guolic1/AirDAP/firmware/components/ota_manager/ota_manager.c

#include <stdbool.h>
#include <stddef.h>
#include <stdint.h>
#include <string.h>

#include "airdap_dap_ownership.h"
#include "airdap_device_identity.h"
#include "airdap_mode_state.h"
#include "airdap_ota.h"
#include "airdap_target_uart.h"
#include "freertos/FreeRTOS.h"
#include "freertos/semphr.h"
#include "esp_err.h"
#include "esp_ota_ops.h"
#include "esp_partition.h"
#include "esp_system.h"

typedef enum {
    OTA_SESSION_IDLE,
    OTA_SESSION_RECEIVING,
    OTA_SESSION_COMMITTED,
} ota_session_state_t;

typedef struct {
    const esp_partition_t *partition;
    esp_ota_handle_t handle;
    uint32_t expected_size;
    uint32_t written_size;
    ota_session_state_t state;
    void *connection;
    uint32_t owner_session;
    bool disconnected;
} ota_session_t;

static ota_session_t session;
static SemaphoreHandle_t session_mutex;

static bool lock_session(void)
{
    return session_mutex != NULL && xSemaphoreTake(session_mutex, portMAX_DELAY) == pdTRUE;
}

static void unlock_session(void)
{
    (void) xSemaphoreGive(session_mutex);
}

static bool authorized(const airdap_ota_client_t *client)
{
    return client == NULL || (client->connection != NULL && client->session_id != 0U &&
        client->authorize != NULL && client->authorize(client->connection, client->session_id));
}

static bool owns_session(const airdap_ota_client_t *client)
{
    return session.connection == (client == NULL ? NULL : client->connection) &&
        session.owner_session == (client == NULL ? 0U : client->session_id);
}

static void reset_session(void)
{
    memset(&session, 0, sizeof(session));
    session.state = OTA_SESSION_IDLE;
}

static bool restore_idle_mode(airdap_mode_event_t event)
{
    const airdap_mode_state_result_t mode_result =
        airdap_mode_state_transition(event);
    if (mode_result != AIRDAP_MODE_STATE_OK) {
        return false;
    }
    const airdap_dap_ownership_result_t ownership_result =
        airdap_dap_ownership_resume();
    return ownership_result == AIRDAP_DAP_OWNERSHIP_OK &&
        airdap_target_uart_resume() == ESP_OK;
}

static esp_err_t initialize_locked(void)
{
    esp_err_t abort_error = ESP_OK;
    if (session.state == OTA_SESSION_RECEIVING) {
        abort_error = esp_ota_abort(session.handle);
    }
    reset_session();
    if (airdap_mode_state_transition(AIRDAP_MODE_EVENT_OTA_RESET) !=
        AIRDAP_MODE_STATE_OK) {
        return ESP_ERR_INVALID_STATE;
    }
    const airdap_dap_ownership_result_t ownership_result =
        airdap_dap_ownership_resume();
    if (ownership_result != AIRDAP_DAP_OWNERSHIP_OK &&
        ownership_result != AIRDAP_DAP_OWNERSHIP_INVALID_STATE) {
        return ESP_ERR_INVALID_STATE;
    }
    return airdap_target_uart_resume() == ESP_OK ? abort_error : ESP_FAIL;
}

static bool debug_allowed_locked(void)
{
    airdap_mode_snapshot_t mode;
    return session.state == OTA_SESSION_IDLE &&
        airdap_mode_state_get(&mode) == AIRDAP_MODE_STATE_OK &&
        mode.ota == AIRDAP_OTA_IDLE;
}

static airdap_ota_status_t get_info_locked(airdap_ota_info_t *info)
{
    if (info == NULL) {
        return AIRDAP_OTA_STATUS_INVALID_ARGUMENT;
    }

    const esp_partition_t *partition = esp_ota_get_next_update_partition(NULL);
    const airdap_device_identity_t *identity = airdap_device_identity_get();
    if (partition == NULL || identity == NULL || partition->size > UINT32_MAX) {
        return AIRDAP_OTA_STATUS_INTERNAL_ERROR;
    }

    memset(info, 0, sizeof(*info));
    const esp_partition_t *running = esp_ota_get_running_partition();
    esp_ota_img_states_t running_state;
    if (running == NULL || esp_ota_get_state_partition(running, &running_state) != ESP_OK) {
        return AIRDAP_OTA_STATUS_INTERNAL_ERROR;
    }
    info->running_address = running->address;
    info->update_address = partition->address;
    info->running_valid = running_state == ESP_OTA_IMG_VALID;
    info->protocol_version = AIRDAP_OTA_PROTOCOL_VERSION;
    info->flags = AIRDAP_OTA_FLAG_ROLLBACK;
    info->max_image_size = (uint32_t) partition->size;
    size_t version_length = 0U;
    while (version_length < AIRDAP_OTA_VERSION_CAPACITY &&
           identity->firmware_version[version_length] != '\0') {
        ++version_length;
    }
    memcpy(info->running_version, identity->firmware_version, version_length);
    info->running_version[version_length] = '\0';
    return AIRDAP_OTA_STATUS_OK;
}

static airdap_ota_status_t begin_locked(const airdap_ota_client_t *client, uint32_t image_size)
{
    if (session.state != OTA_SESSION_IDLE) {
        return AIRDAP_OTA_STATUS_INVALID_STATE;
    }

    const esp_partition_t *partition = esp_ota_get_next_update_partition(NULL);
    if (partition == NULL || partition->size > UINT32_MAX) {
        return AIRDAP_OTA_STATUS_INTERNAL_ERROR;
    }
    if (image_size == 0U || image_size > partition->size) {
        return AIRDAP_OTA_STATUS_INVALID_SIZE;
    }

    if (airdap_mode_state_transition(AIRDAP_MODE_EVENT_OTA_STARTED) !=
        AIRDAP_MODE_STATE_OK) {
        return AIRDAP_OTA_STATUS_INTERNAL_ERROR;
    }

    const airdap_dap_ownership_result_t ownership_result =
        airdap_dap_ownership_suspend();
    if (ownership_result == AIRDAP_DAP_OWNERSHIP_BUSY) {
        return airdap_mode_state_transition(AIRDAP_MODE_EVENT_OTA_FAILED) ==
            AIRDAP_MODE_STATE_OK
            ? AIRDAP_OTA_STATUS_INVALID_STATE
            : AIRDAP_OTA_STATUS_INTERNAL_ERROR;
    }
    if (ownership_result != AIRDAP_DAP_OWNERSHIP_OK) {
        if (airdap_mode_state_transition(AIRDAP_MODE_EVENT_OTA_FAILED) !=
            AIRDAP_MODE_STATE_OK) {
            return AIRDAP_OTA_STATUS_INTERNAL_ERROR;
        }
        return AIRDAP_OTA_STATUS_INTERNAL_ERROR;
    }

    if (airdap_target_uart_suspend() != ESP_OK) {
        (void) restore_idle_mode(AIRDAP_MODE_EVENT_OTA_FAILED);
        return AIRDAP_OTA_STATUS_BUSY;
    }
    if (!authorized(client)) {
        (void) restore_idle_mode(AIRDAP_MODE_EVENT_OTA_FAILED);
        return AIRDAP_OTA_STATUS_UNAUTHENTICATED;
    }

    esp_ota_handle_t handle = 0U;
    if (esp_ota_begin(
            partition,
            OTA_WITH_SEQUENTIAL_WRITES,
            &handle) != ESP_OK) {
        if (handle != 0U) {
            (void) esp_ota_abort(handle);
        }
        (void) restore_idle_mode(AIRDAP_MODE_EVENT_OTA_FAILED);
        return AIRDAP_OTA_STATUS_INTERNAL_ERROR;
    }

    session.partition = partition;
    session.handle = handle;
    session.expected_size = image_size;
    session.written_size = 0U;
    session.state = OTA_SESSION_RECEIVING;
    session.connection = client == NULL ? NULL : client->connection;
    session.owner_session = client == NULL ? 0U : client->session_id;
    return AIRDAP_OTA_STATUS_OK;
}

static airdap_ota_status_t write_locked(
    uint32_t offset,
    const void *data,
    size_t size,
    uint32_t *next_offset)
{
    if (session.state != OTA_SESSION_RECEIVING) {
        return AIRDAP_OTA_STATUS_INVALID_STATE;
    }
    if (data == NULL || next_offset == NULL) {
        return AIRDAP_OTA_STATUS_INVALID_ARGUMENT;
    }
    if (offset != session.written_size) {
        return AIRDAP_OTA_STATUS_INVALID_OFFSET;
    }
    if (size == 0U || size > session.expected_size - session.written_size) {
        return AIRDAP_OTA_STATUS_INVALID_SIZE;
    }

    if (esp_ota_write(session.handle, data, size) != ESP_OK) {
        if (esp_ota_abort(session.handle) != ESP_OK) {
            return AIRDAP_OTA_STATUS_INTERNAL_ERROR;
        }
        reset_session();
        return restore_idle_mode(AIRDAP_MODE_EVENT_OTA_FAILED)
            ? AIRDAP_OTA_STATUS_WRITE_FAILED
            : AIRDAP_OTA_STATUS_INTERNAL_ERROR;
    }

    session.written_size += (uint32_t) size;
    *next_offset = session.written_size;
    return AIRDAP_OTA_STATUS_OK;
}

static airdap_ota_status_t commit_locked(const airdap_ota_client_t *client)
{
    if (session.state != OTA_SESSION_RECEIVING) {
        return AIRDAP_OTA_STATUS_INVALID_STATE;
    }
    if (session.written_size != session.expected_size) {
        return AIRDAP_OTA_STATUS_INCOMPLETE_IMAGE;
    }

    const esp_partition_t *partition = session.partition;
    const esp_ota_handle_t handle = session.handle;
    if (esp_ota_end(handle) != ESP_OK) {
        reset_session();
        return restore_idle_mode(AIRDAP_MODE_EVENT_OTA_FAILED)
            ? AIRDAP_OTA_STATUS_VALIDATION_FAILED
            : AIRDAP_OTA_STATUS_INTERNAL_ERROR;
    }
    if (!authorized(client)) {
        reset_session();
        (void) restore_idle_mode(AIRDAP_MODE_EVENT_OTA_FAILED);
        return AIRDAP_OTA_STATUS_UNAUTHENTICATED;
    }
    if (esp_ota_set_boot_partition(partition) != ESP_OK) {
        reset_session();
        return restore_idle_mode(AIRDAP_MODE_EVENT_OTA_FAILED)
            ? AIRDAP_OTA_STATUS_ACTIVATION_FAILED
            : AIRDAP_OTA_STATUS_INTERNAL_ERROR;
    }

    session.partition = partition;
    session.handle = 0U;
    session.expected_size = 0U;
    session.written_size = 0U;
    session.state = OTA_SESSION_COMMITTED;
    if (airdap_mode_state_transition(AIRDAP_MODE_EVENT_OTA_COMMITTED) !=
        AIRDAP_MODE_STATE_OK) {
        return AIRDAP_OTA_STATUS_INTERNAL_ERROR;
    }
    return AIRDAP_OTA_STATUS_OK;
}

static airdap_ota_status_t abort_locked(void)
{
    if (session.state == OTA_SESSION_IDLE) {
        return AIRDAP_OTA_STATUS_OK;
    }
    if (session.state == OTA_SESSION_COMMITTED) {
        return AIRDAP_OTA_STATUS_INVALID_STATE;
    }

    const esp_err_t error = esp_ota_abort(session.handle);
    if (error != ESP_OK) {
        return AIRDAP_OTA_STATUS_INTERNAL_ERROR;
    }
    reset_session();
    return restore_idle_mode(AIRDAP_MODE_EVENT_OTA_ABORTED)
        ? AIRDAP_OTA_STATUS_OK
        : AIRDAP_OTA_STATUS_INTERNAL_ERROR;
}

static airdap_ota_status_t reboot_locked(void)
{
    if (session.state != OTA_SESSION_COMMITTED) {
        return AIRDAP_OTA_STATUS_INVALID_STATE;
    }
    esp_restart();
    return AIRDAP_OTA_STATUS_OK;
}

esp_err_t airdap_ota_confirm_running_image(void)
{
    const esp_partition_t *running = esp_ota_get_running_partition();
    if (running == NULL) {
        return ESP_FAIL;
    }

    esp_ota_img_states_t state;
    const esp_err_t error = esp_ota_get_state_partition(running, &state);
    if (error != ESP_OK) {
        return error;
    }
    if (state == ESP_OTA_IMG_PENDING_VERIFY) {
        return esp_ota_mark_app_valid_cancel_rollback();
    }
    return ESP_OK;
}

esp_err_t airdap_ota_initialize(void)
{
    /* Called once by app_main before transports start. */
    if (session_mutex == NULL) session_mutex = xSemaphoreCreateMutex();
    if (!lock_session()) return ESP_FAIL;
    const esp_err_t result = initialize_locked();
    unlock_session();
    return result;
}

bool airdap_ota_debug_allowed(void)
{
    if (!lock_session()) return false;
    const bool result = debug_allowed_locked();
    unlock_session();
    return result;
}

airdap_ota_status_t airdap_ota_get_info(airdap_ota_info_t *info)
{
    if (!lock_session()) return AIRDAP_OTA_STATUS_INTERNAL_ERROR;
    const airdap_ota_status_t result = get_info_locked(info);
    unlock_session();
    return result;
}

airdap_ota_status_t airdap_ota_begin_for_client(
    const airdap_ota_client_t *client, uint32_t image_size)
{
    if (!lock_session()) return AIRDAP_OTA_STATUS_INTERNAL_ERROR;
    airdap_ota_status_t result;
    if (!authorized(client)) result = AIRDAP_OTA_STATUS_UNAUTHENTICATED;
    else if (session.state != OTA_SESSION_IDLE && !owns_session(client)) result = AIRDAP_OTA_STATUS_BUSY;
    else result = begin_locked(client, image_size);
    unlock_session();
    return result;
}

airdap_ota_status_t airdap_ota_begin(uint32_t image_size)
{
    return airdap_ota_begin_for_client(NULL, image_size);
}

airdap_ota_status_t airdap_ota_write_for_client(
    const airdap_ota_client_t *client, uint32_t offset, const void *data, size_t size, uint32_t *next_offset)
{
    if (!lock_session()) return AIRDAP_OTA_STATUS_INTERNAL_ERROR;
    airdap_ota_status_t result;
    if (!authorized(client)) result = AIRDAP_OTA_STATUS_UNAUTHENTICATED;
    else if (session.state != OTA_SESSION_IDLE && !owns_session(client)) result = AIRDAP_OTA_STATUS_BUSY;
    else result = write_locked(offset, data, size, next_offset);
    unlock_session();
    return result;
}

airdap_ota_status_t airdap_ota_write(uint32_t offset, const void *data, size_t size, uint32_t *next_offset)
{
    return airdap_ota_write_for_client(NULL, offset, data, size, next_offset);
}

airdap_ota_status_t airdap_ota_commit_for_client(
    const airdap_ota_client_t *client)
{
    if (!lock_session()) return AIRDAP_OTA_STATUS_INTERNAL_ERROR;
    airdap_ota_status_t result;
    if (!authorized(client)) result = AIRDAP_OTA_STATUS_UNAUTHENTICATED;
    else if (session.state != OTA_SESSION_IDLE && !owns_session(client)) result = AIRDAP_OTA_STATUS_BUSY;
    else result = commit_locked(client);
    unlock_session();
    return result;
}

airdap_ota_status_t airdap_ota_commit(void)
{
    return airdap_ota_commit_for_client(NULL);
}

airdap_ota_status_t airdap_ota_abort_for_client(
    const airdap_ota_client_t *client)
{
    if (!lock_session()) return AIRDAP_OTA_STATUS_INTERNAL_ERROR;
    airdap_ota_status_t result;
    if (!authorized(client)) result = AIRDAP_OTA_STATUS_UNAUTHENTICATED;
    else if (session.state != OTA_SESSION_IDLE && !owns_session(client) && !session.disconnected) result = AIRDAP_OTA_STATUS_BUSY;
    else result = abort_locked();
    unlock_session();
    return result;
}

airdap_ota_status_t airdap_ota_abort(void)
{
    return airdap_ota_abort_for_client(NULL);
}

airdap_ota_status_t airdap_ota_reboot_for_client(
    const airdap_ota_client_t *client)
{
    if (!lock_session()) return AIRDAP_OTA_STATUS_INTERNAL_ERROR;
    airdap_ota_status_t result;
    if (!authorized(client)) result = AIRDAP_OTA_STATUS_UNAUTHENTICATED;
    else result = reboot_locked();
    unlock_session();
    return result;
}

airdap_ota_status_t airdap_ota_reboot(void)
{
    return airdap_ota_reboot_for_client(NULL);
}

airdap_ota_status_t airdap_ota_disconnect_client(const airdap_ota_client_t *client)
{
    if (!lock_session()) return AIRDAP_OTA_STATUS_INTERNAL_ERROR;
    airdap_ota_status_t result = AIRDAP_OTA_STATUS_OK;
    if (session.state == OTA_SESSION_RECEIVING && owns_session(client)) {
        session.disconnected = true;
        result = abort_locked();
        /* Failed cleanup remains blocked, but a new authorized client may
         * retry ABORT after the old TLS connection has been destroyed. */
    }
    unlock_session();
    return result;
}

void airdap_ota_handle_disconnect(void)
{
    (void) airdap_ota_disconnect_client(NULL);
}

airdap_ota_status_t airdap_ota_prepare_reboot(const airdap_ota_client_t *client)
{
    if (!lock_session()) return AIRDAP_OTA_STATUS_INTERNAL_ERROR;
    const airdap_ota_status_t result = !authorized(client)
        ? AIRDAP_OTA_STATUS_UNAUTHENTICATED
        : session.state == OTA_SESSION_COMMITTED
        ? AIRDAP_OTA_STATUS_OK : AIRDAP_OTA_STATUS_INVALID_STATE;
    unlock_session();
    return result;
}
