guolic1/AirDAP/firmware/components/board/include/airdap_board.h

#pragma once

#include <stdbool.h>

#include "esp_err.h"

#ifdef __cplusplus
extern "C" {
#endif

/* Reacquire all target-facing pins in their non-invasive startup state. */
esp_err_t airdap_board_init_safe(void);

/*
 * Release or pull low the shared TPS2116 ST / TPS22919 ON network.
 * "Allowed" means the external open-drain status circuit may enable target
 * power; it does not guarantee that USB is selected or that VTref is present.
 */
esp_err_t airdap_target_power_set_allowed(bool allowed);
esp_err_t airdap_target_power_get_active(bool *active);
/* Last successful output command, independent of the shared ST input level. */
bool airdap_target_power_is_allowed(void);

/* GPIO41 drives an inverting transistor: high asserts target nRESET. */
esp_err_t airdap_target_reset_set_asserted(bool asserted);

/* Last successful GPIO command, not a measurement of target NRST. */
bool airdap_target_reset_is_asserted(void);

/* BOOT_KEY is active low and doubles as the ROM download-mode strap. */
esp_err_t airdap_boot_key_get_pressed(bool *pressed);

/* Development-only RAM input used by USB HIL control. It is combined with the
 * physical level and remains set until explicitly released or rebooted. */
esp_err_t airdap_boot_key_set_simulated_pressed(bool pressed);
esp_err_t airdap_boot_key_get_simulated_pressed(bool *pressed);

/* Hide the active-low board wiring from user-visible LED state changes. */
esp_err_t airdap_board_leds_set(bool status_on, bool network_on);

#ifdef __cplusplus
}
#endif
