guolic1/AirDAP/host/src/lib.rs

//! Native AirDAP host service and protocol implementation.
pub mod credential;
pub mod mount;
pub mod network;
pub mod ota;
pub mod provisioning;
pub mod security2;
pub mod service;
pub mod store;
pub mod usb;
pub mod usbip;
pub mod web;
