guolic1/AirDAP/firmware/test/unit/usb_uart_bridge/test_usb_uart_bridge.c

#include <assert.h>
#include <setjmp.h>
#include <stdbool.h>
#include <stddef.h>
#include <stdint.h>
#include <stdio.h>
#include <string.h>

#include "airdap_target_uart.h"
#include "airdap_usb_uart_bridge.h"
#include "freertos/task.h"
#include "tinyusb_cdc_acm.h"
#include "tusb.h"

enum {
    USB_UART_TASK_STACK_SIZE = 3072,
    USB_UART_TASK_PRIORITY = 5,
};

static tinyusb_config_cdcacm_t cdc_config;
static esp_err_t cdc_init_result = ESP_OK;
static TaskFunction_t bridge_task;
static BaseType_t task_create_result = pdPASS;
static unsigned int task_create_calls;
static TickType_t last_delay;
static jmp_buf worker_yield;
static bool cdc_connected;
static bool data_ready = true;
bool airdap_usb_data_ready(void) { return data_ready; }
static uint8_t cdc_input[32];
static size_t cdc_input_length;
static unsigned int cdc_read_calls;
static uint8_t cdc_output[32];
static size_t cdc_output_length;
static uint32_t cdc_write_available = sizeof(cdc_output);
static size_t cdc_queue_limit = sizeof(cdc_output);
static unsigned int cdc_flush_calls;

static airdap_target_uart_session_id_t next_session = 41U;
static airdap_target_uart_session_id_t live_session;
static airdap_target_uart_session_id_t owner_session;
static airdap_target_uart_result_t open_result = AIRDAP_TARGET_UART_OK;
static unsigned int open_calls;
static unsigned int close_calls;
static unsigned int acquire_calls;
static unsigned int configure_calls;
static unsigned int service_read_calls;
static unsigned int service_write_calls;
static cdc_line_coding_t configured_line_coding;
static uint8_t service_rx[32];
static size_t service_rx_length;
static uint8_t service_tx[32];
static size_t service_tx_length;

BaseType_t xTaskCreatePinnedToCore(
    TaskFunction_t task,
    const char *name,
    uint32_t stack_depth,
    void *argument,
    UBaseType_t priority,
    TaskHandle_t *handle,
    BaseType_t core_id)
{
    assert(task != NULL && strcmp(name, "usb_uart") == 0);
    assert(stack_depth == USB_UART_TASK_STACK_SIZE);
    assert(argument == NULL && priority == USB_UART_TASK_PRIORITY);
    assert(handle == NULL && core_id == 1);
    ++task_create_calls;
    bridge_task = task;
    return task_create_result;
}

void vTaskDelay(TickType_t ticks)
{
    last_delay = ticks;
    longjmp(worker_yield, 1);
}

esp_err_t tinyusb_cdcacm_init(const tinyusb_config_cdcacm_t *config)
{
    assert(config != NULL);
    cdc_config = *config;
    return cdc_init_result;
}

esp_err_t tinyusb_cdcacm_read(
    int interface_number,
    uint8_t *data,
    size_t capacity,
    size_t *received)
{
    assert(interface_number == 0 && data != NULL && received != NULL);
    ++cdc_read_calls;
    const size_t count = capacity < cdc_input_length
        ? capacity
        : cdc_input_length;
    memcpy(data, cdc_input, count);
    memmove(cdc_input, cdc_input + count, cdc_input_length - count);
    cdc_input_length -= count;
    *received = count;
    return ESP_OK;
}

size_t tinyusb_cdcacm_write_queue(
    tinyusb_cdcacm_itf_t interface_number,
    const uint8_t *data,
    size_t length)
{
    assert(interface_number == TINYUSB_CDC_ACM_0 && data != NULL);
    const size_t count = length < cdc_queue_limit ? length : cdc_queue_limit;
    memcpy(cdc_output, data, count);
    cdc_output_length = count;
    return count;
}

esp_err_t tinyusb_cdcacm_write_flush(
    tinyusb_cdcacm_itf_t interface_number,
    uint32_t timeout_ticks)
{
    assert(interface_number == TINYUSB_CDC_ACM_0 && timeout_ticks == 0U);
    ++cdc_flush_calls;
    return ESP_OK;
}

bool tud_cdc_n_connected(uint8_t interface_number)
{
    assert(interface_number == 0U);
    return cdc_connected;
}

uint32_t tud_cdc_n_write_available(uint8_t interface_number)
{
    assert(interface_number == 0U);
    return cdc_write_available;
}
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
